TeHSiGGi/agp-power-monitor/pictures/apm_dongles.jpg

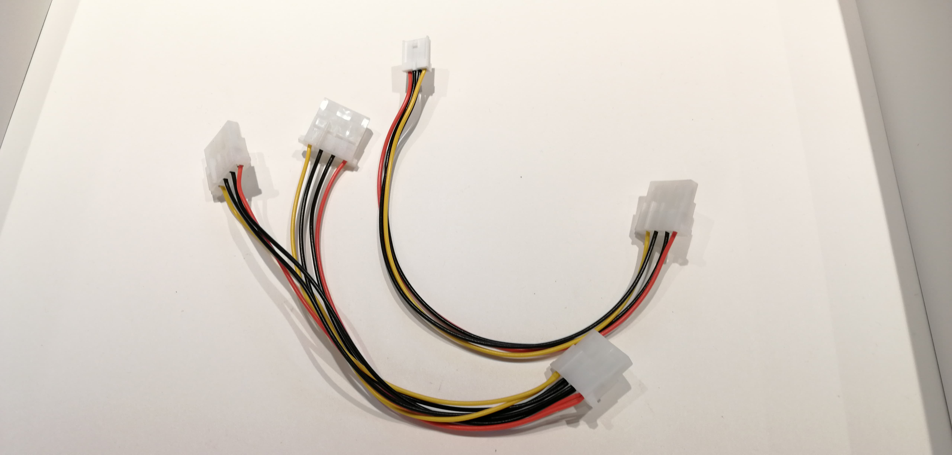
pictures/apm_dongles.jpg
