TeHSiGGi/agp-power-monitor/pictures/apm_in_use.jpg

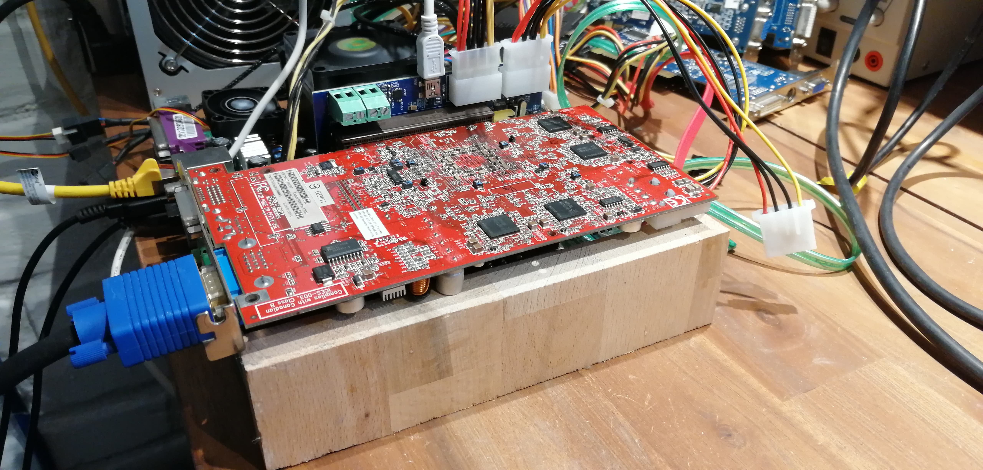
pictures/apm_in_use.jpg
